jjhcwoo/mse320-project/Vertical Bar.SLDPRT

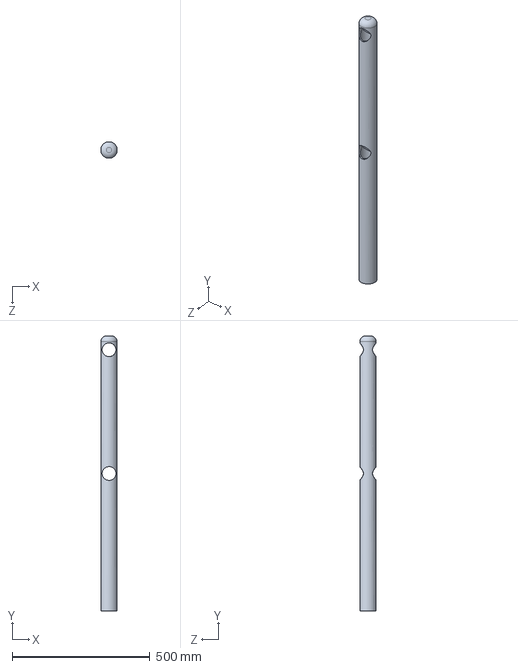
[picture p11: CAD file, 2025-12-01]
Vertical Bar.SLDPRT
60.0 x 1000.0 x 60.0 mm
