jjhcwoo/mse320-project/hole.SLDPRT

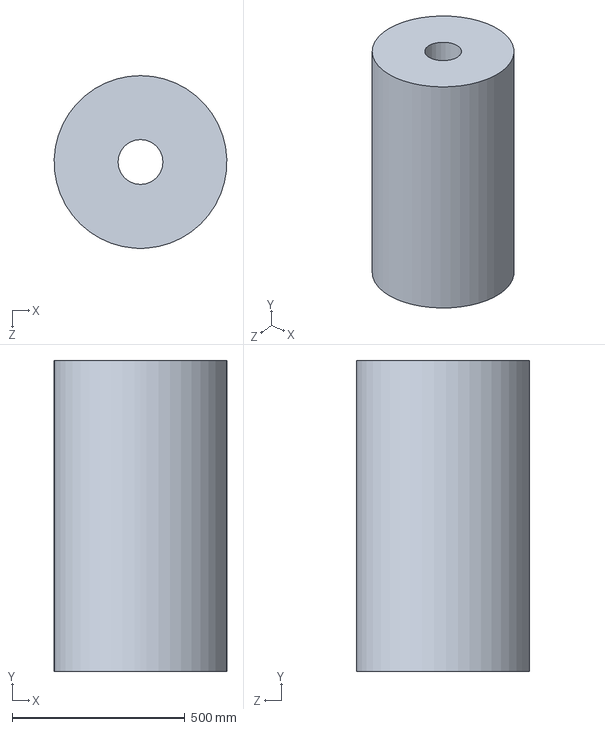
[picture p12: CAD file, 2025-12-01]
hole.SLDPRT
499.7 x 900.0 x 500.0 mm
